Dennis-van-Gils/project-WiFi-Chemicals-Delivery-Bell/docs/photos/02_chemicals_bell__side.jpg

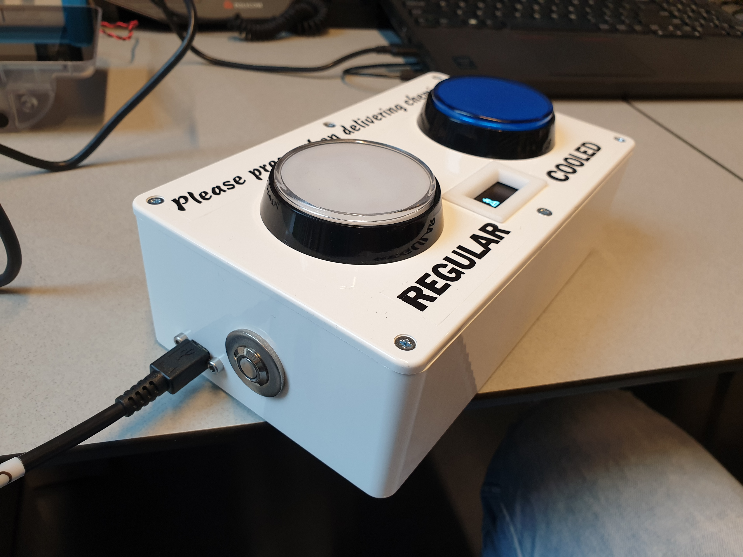
docs/photos/02_chemicals_bell__side.jpg
