Dennis-van-Gils/project-WiFi-Chemicals-Delivery-Bell/docs/photos/03_chemicals_bell__starting_up.jpg

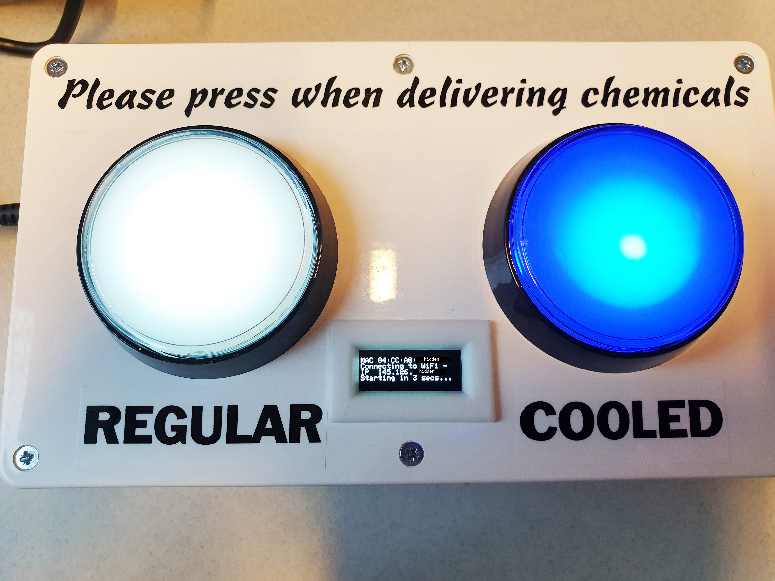
docs/photos/03_chemicals_bell__starting_up.jpg
