Dennis-van-Gils/project-WiFi-Chemicals-Delivery-Bell/docs/photos/05_chemicals_bell__opened.jpg

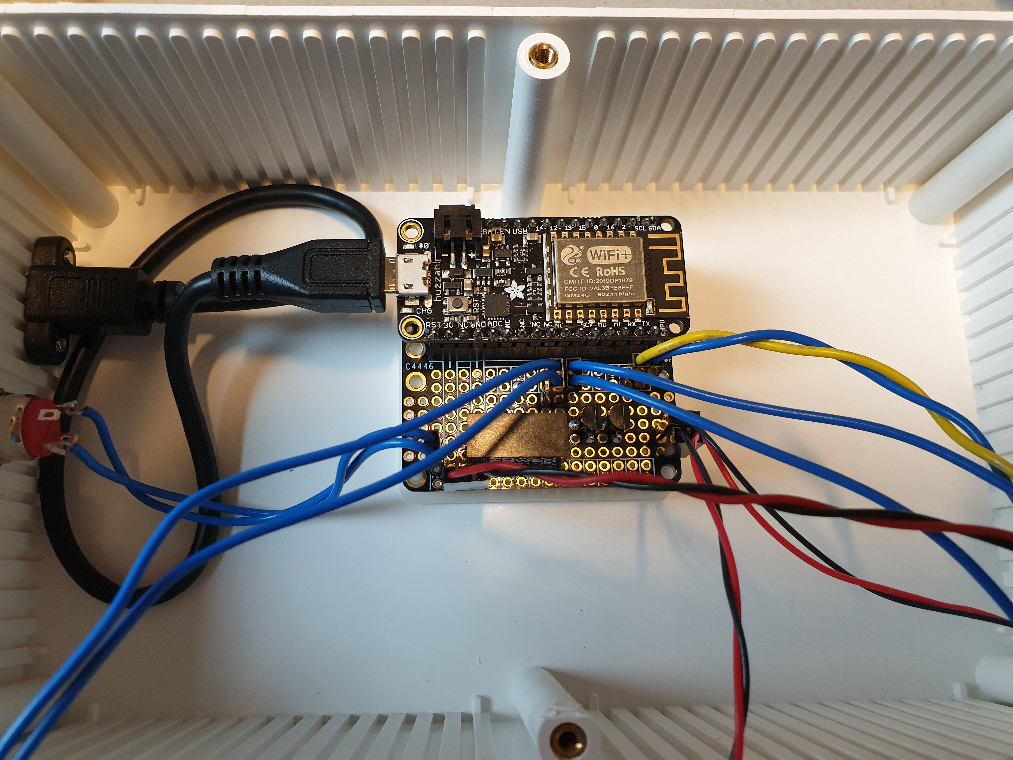
docs/photos/05_chemicals_bell__opened.jpg
