Dennis-van-Gils/project-WiFi-Chemicals-Delivery-Bell/docs/photos/07_detail__screen.jpg

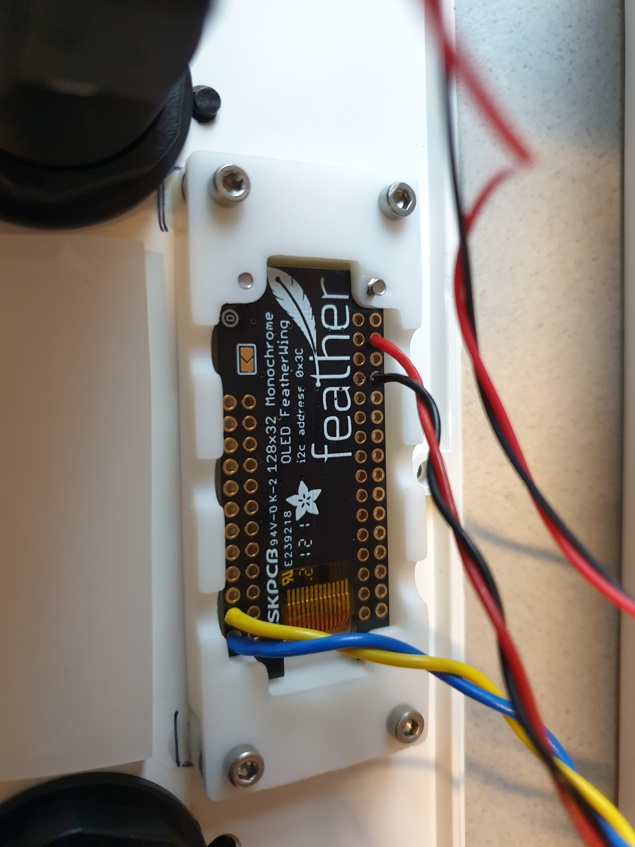
docs/photos/07_detail__screen.jpg
