Dennis-van-Gils/project-WiFi-Chemicals-Delivery-Bell/web/chemicals_delivery/android-chrome-192x192.png

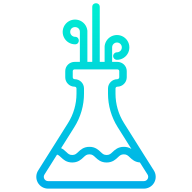
web/chemicals_delivery/android-chrome-192x192.png
