Dennis-van-Gils/project-WiFi-Chemicals-Delivery-Bell/docs/photos/12_assembly.jpg

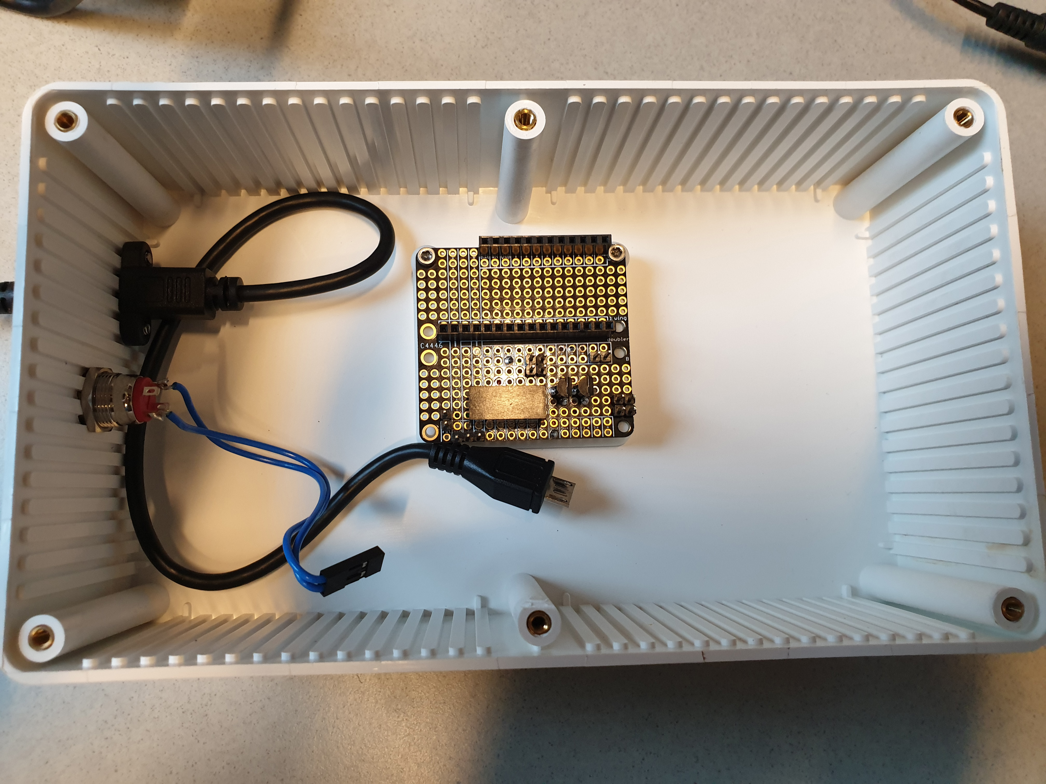
docs/photos/12_assembly.jpg
