Dennis-van-Gils/project-WiFi-Chemicals-Delivery-Bell/docs/photos/13_assembly.jpg

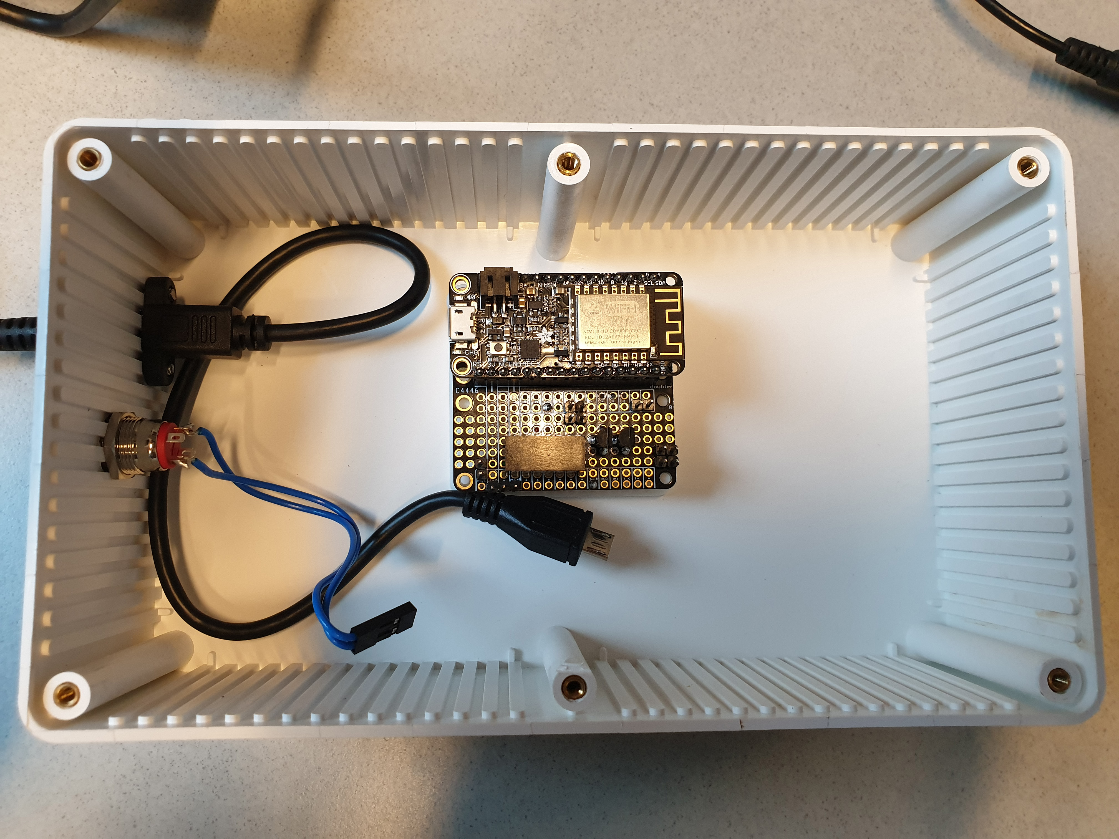
docs/photos/13_assembly.jpg
