Dennis-van-Gils/project-WiFi-Chemicals-Delivery-Bell/source_mcu/src/wifi_settings_template.h

#ifndef WIFI_SETTINGS_H
#define WIFI_SETTINGS_H

/* `wifi_settings.h` should contain the user variables specific to your WiFi
network, password and webpage script locations. You can use the provided
template `wifi_settings_template.h` to fill out your settings and save as
`wifi_settings.h`. You need to compile and upload this source code to the
Arduino whenever you make changes to it.
*/

/* The SSID of the WiFi network that the Arduino should connect to.
E.g. "UThings" for the University of Twente.
*/
const char *ssid = "";

/* Specific to the UThings network (and perhaps other IoT networks as well):
The Arduino should get a unique 'pre-shared key' password from the network
administrator (LISA). This is needed to allow the Arduino easy access to the
UThings network. You need to give LISA the MAC address of your Arduino. They
will then couple this MAC address with a unique key which they will send to you.
Keep this password secret.

To get the MAC address of the Arduino you can upload this source code to the
Arduino and leave the password blank. Both the OLED display and a serial
monitor (like PuTTY for Windows) will then show you the MAC address at startup
of the Arduino.
*/
const char *password = "";

/* The URL to your website serving the chemicals delivery application.
E.g. "https://pof-inventory.tnw.utwente.nl/chemicals_delivery"
*/
const char *url_website = "";

/* An automated email will be send out to the users after each button press.
However, to prevent spam there is a delay timer before the email gets send out.
This allows the user to revert back an (erroneous) button push and prevents an
email from being send out if the state has reverted back to its previous state
in the mean time.

The users that will receive an email are configured on the web server, see and
edit `globals.php` on the server.
*/
const float EMAIL_DELAY_MINUTES = 1;

#endif
